AguuSz/Proyecto-2018/Imagenes/1.jpeg

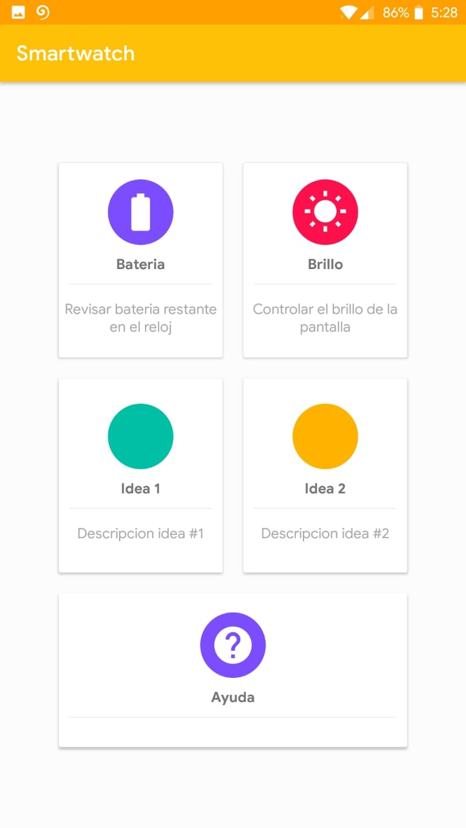
Imagenes/1.jpeg
