AguuSz/Proyecto-2018/Imagenes/3.jpeg

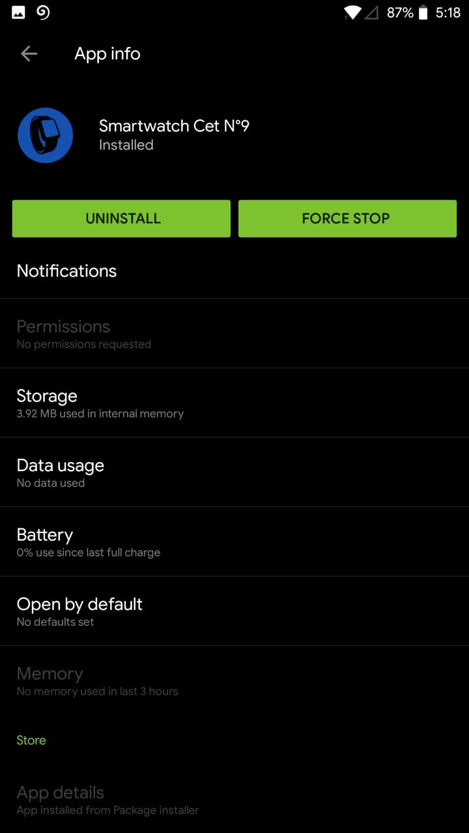
Imagenes/3.jpeg
