AguuSz/Proyecto-2018/Imagenes/noun_Smart Watch_75426.png

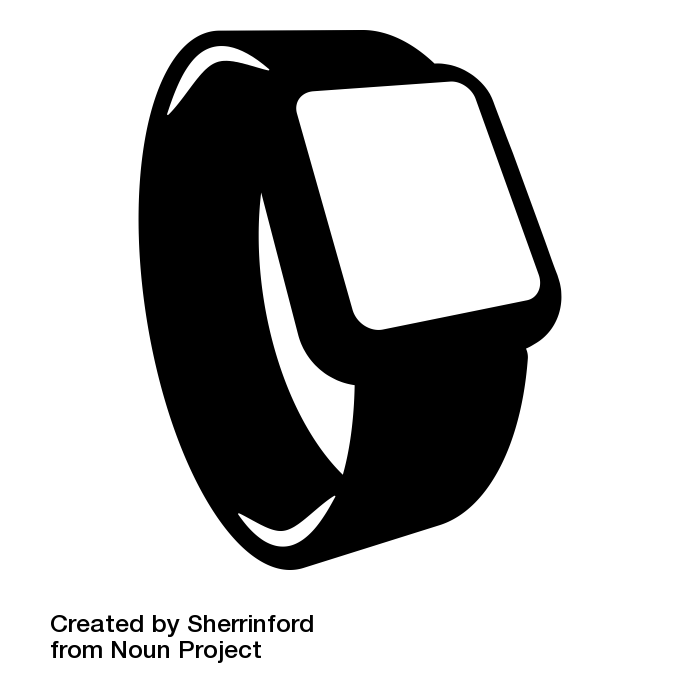
Imagenes/noun_Smart Watch_75426.png
