AguuSz/Proyecto-2018/Imagenes/Screenshot codigo.png

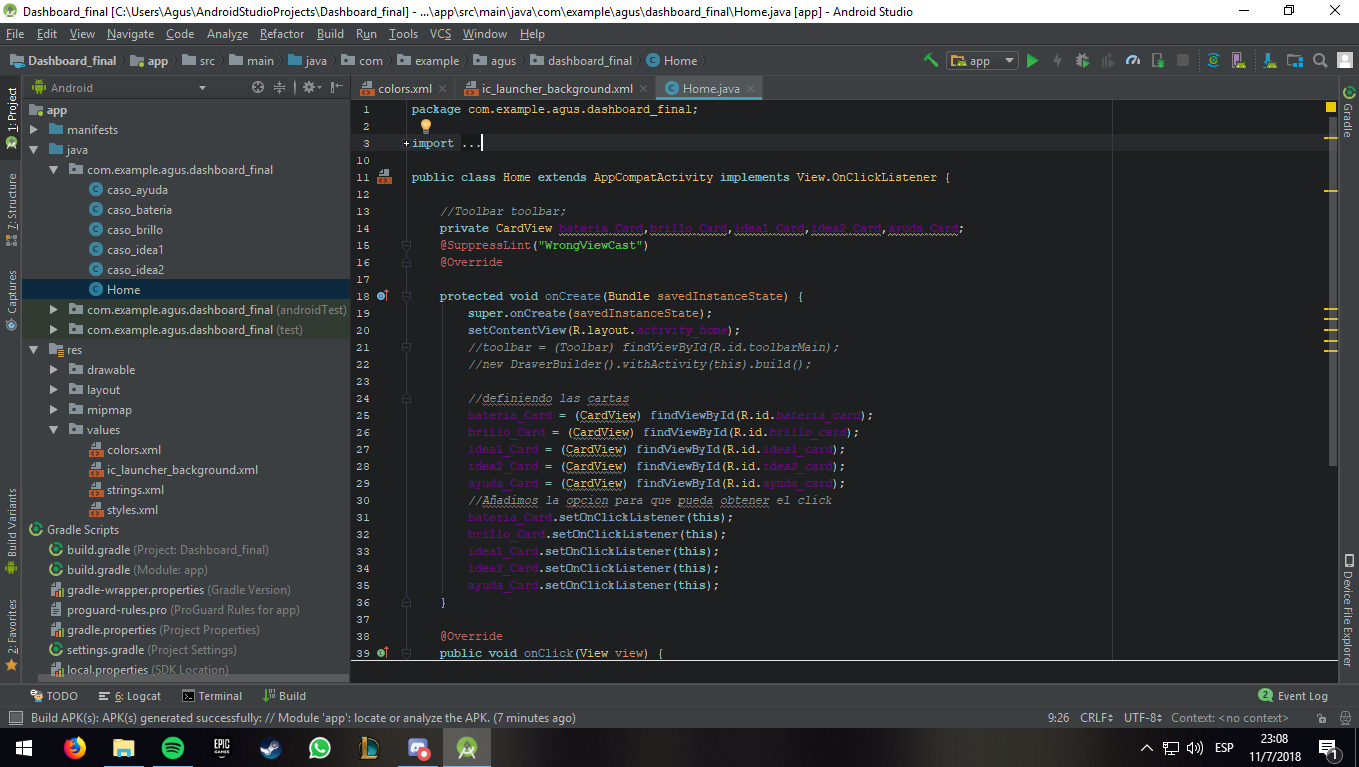
Imagenes/Screenshot codigo.png
